Junkotron/Flurp_Zx81/src/keyboard.v

// ZX Spectrum for Altera DE1
//
// Copyright (c) 2009-2011 Mike Stirling
// Copyright (c) 2015-2017 Sorgelig
//
// All rights reserved
//
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
// * Redistributions in synthesized form must reproduce the above copyright
//   notice, this list of conditions and the following disclaimer in the
//   documentation and/or other materials provided with the distribution.
//
// * Neither the name of the author nor the names of other contributors may
//   be used to endorse or promote products derived from this software without
//   specific prior written agreement from the author.
//
// * License is granted for non-commercial use only.  A fee may not be charged
//   for redistributions as source code or in synthesized/hardware form without 
//   specific prior written agreement from the author.
//
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

// PS/2 scancode to Spectrum matrix conversionmodule keyboard
module keyboard
  (
   input 	     reset,
   input 	     clk_sys,

   input [10:0]      ps2_key,

   input [15:0]      addr,
   output [4:0]      key_data,

   output reg [11:1] Fn = 0,
   output reg [2:0]  mod = 0,

   // Remote control via serial
   input 	     strobe=0,
   input 	     press,
   input [2:0] 	     row,
   input [2:0] 	     col,
   
   );

   reg [4:0] 	     keys[7:0];
   reg 		     release_btn = 0;
   reg [7:0] 	     code;

   reg 		     old_strobe=0;
   
   // Output addressed row to ULA
   assign key_data = (!addr[8]  ? keys[0] : 5'b11111)&
		     (!addr[9]  ? keys[1] : 5'b11111)&
		     (!addr[10] ? keys[2] : 5'b11111)&
		     (!addr[11] ? keys[3] : 5'b11111)&
		     (!addr[12] ? keys[4] : 5'b11111)&
		     (!addr[13] ? keys[5] : 5'b11111)&
		     (!addr[14] ? keys[6] : 5'b11111)&
		     (!addr[15] ? keys[7] : 5'b11111);

   reg 		     old_reset = 0;
   
   always @(posedge clk_sys) begin
      old_reset <= reset;
      old_strobe <= strobe;

      if (old_reset != reset) begin
	 keys[0] <= 5'b11111;
	 keys[1] <= 5'b11111;
	 keys[2] <= 5'b11111;
	 keys[3] <= 5'b11111;
	 keys[4] <= 5'b11111;
	 keys[5] <= 5'b11111;
	 keys[6] <= 5'b11111;
	 keys[7] <= 5'b11111;
      end

      if(ps2_key[10]) begin
	 release_btn <= ~ps2_key[9];
	 code <= ps2_key[7:0];
      end
      else if (old_strobe == 0 && strobe==1)
	begin
	   if (col==7) // impossible col (only 5 cols) special meaning
	     begin
		keys[0] <= 5'b11111;
		keys[1] <= 5'b11111;
		keys[2] <= 5'b11111;
		keys[3] <= 5'b11111;
		keys[4] <= 5'b11111;
		keys[5] <= 5'b11111;
		keys[6] <= 5'b11111;
		keys[7] <= 5'b11111;
	     end
	   else
	     keys[row][col]=press;
	end
      else begin

         case(code)

	   // Here are the only "mersy chord" keys currently.
	   // The delete and arrows which actually punches both
	   // shift and zero on the zx keyboard
	   
	   8'h66 :
	     begin
                keys[0][0] <= release_btn; // shift-
		keys[4][0] <= release_btn; // 0
	     end

	   8'h6b :
	     begin
                keys[0][0] <= release_btn; // shift-
		keys[3][4] <= release_btn; // 5 (left arrow)
	     end
	   8'h72 :
	     begin
                keys[0][0] <= release_btn; // shift-
		keys[4][4] <= release_btn; // 6 (down arrow)
	     end
	   8'h75 :
	     begin
                keys[0][0] <= release_btn; // shift-
		keys[4][3] <= release_btn; // 7 (up arrow)
	     end
	   8'h74 :
	     begin
                keys[0][0] <= release_btn; // shift-
		keys[4][2] <= release_btn; // 8 (right arrow)
	     end
	   
	   8'h12, 8'h61, 8'h59 :
             keys[0][0] <= release_btn; // left shift
	   8'h1a : keys[0][1] <= release_btn; // Z
	   8'h22 : keys[0][2] <= release_btn; // X
	   8'h21 : keys[0][3] <= release_btn; // C
	   8'h2a : keys[0][4] <= release_btn; // V

	   8'h1c : keys[1][0] <= release_btn; // A
	   8'h1b : keys[1][1] <= release_btn; // S
	   8'h23 : keys[1][2] <= release_btn; // D
	   8'h2b : keys[1][3] <= release_btn; // F
	   8'h34 : keys[1][4] <= release_btn; // G

	   8'h15 : keys[2][0] <= release_btn; // Q
	   8'h1d : keys[2][1] <= release_btn; // W
	   8'h24 : keys[2][2] <= release_btn; // E
	   8'h2d : keys[2][3] <= release_btn; // R
	   8'h2c : keys[2][4] <= release_btn; // T

	   8'h16 : keys[3][0] <= release_btn; // 1
	   8'h1e : keys[3][1] <= release_btn; // 2
	   8'h26 : keys[3][2] <= release_btn; // 3
	   8'h25 : keys[3][3] <= release_btn; // 4
	   8'h2e : keys[3][4] <= release_btn; // 5

	   8'h45 : keys[4][0] <= release_btn; // 0
	   8'h46 : keys[4][1] <= release_btn; // 9
	   8'h3e : keys[4][2] <= release_btn; // 8
	   8'h3d : keys[4][3] <= release_btn; // 7
	   8'h36 : keys[4][4] <= release_btn; // 6

	   8'h4d : keys[5][0] <= release_btn; // P
	   8'h44 : keys[5][1] <= release_btn; // O
	   8'h43 : keys[5][2] <= release_btn; // I
	   8'h3c : keys[5][3] <= release_btn; // U
	   8'h35 : keys[5][4] <= release_btn; // Y

	   8'h5a, 8'h4c :
	     keys[6][0] <= release_btn; // ENTER
	   8'h4b : keys[6][1] <= release_btn; // L
	   8'h42 : keys[6][2] <= release_btn; // K
	   8'h3b : keys[6][3] <= release_btn; // J
	   8'h33 : keys[6][4] <= release_btn; // H

	   8'h29, 8'h49 :
             keys[7][0] <= release_btn; // SPACE
	   8'h41 : keys[7][1] <= release_btn; // .
	   8'h3a : keys[7][2] <= release_btn; // M
	   8'h31 : keys[7][3] <= release_btn; // N
	   8'h32 : keys[7][4] <= release_btn; // B
	   
	 endcase
      end
      
   end
endmodule
